sensebox/senseBox-MCU-S2-ESP32S2/examples/icm20948/icm20948.ino

/***************************************************************************
* Example sketch for the ICM20948_WE library
*
* This sketch shows how to setup the accelerometer and how to query accelerometer
* related data. 
* 
* Further information can be found on:
*
* https://wolles-elektronikkiste.de/icm-20948-9-achsensensor-teil-i (German)
* https://wolles-elektronikkiste.de/en/icm-20948-9-axis-sensor-part-i (English)
* 
***************************************************************************/

#include <Wire.h>
#include <ICM20948_WE.h>
#define ICM20948_ADDR 0x68

/* There are several ways to create your ICM20948 object:
 * ICM20948_WE myIMU = ICM20948_WE()              -> uses Wire / I2C Address = 0x68
 * ICM20948_WE myIMU = ICM20948_WE(ICM20948_ADDR) -> uses Wire / ICM20948_ADDR
 * ICM20948_WE myIMU = ICM20948_WE(&wire2)        -> uses the TwoWire object wire2 / ICM20948_ADDR
 * ICM20948_WE myIMU = ICM20948_WE(&wire2, ICM20948_ADDR) -> all together
 * ICM20948_WE myIMU = ICM20948_WE(CS_PIN, spi);  -> uses SPI, spi is just a flag, see SPI example
 * ICM20948_WE myIMU = ICM20948_WE(&SPI, CS_PIN, spi);  -> uses SPI / passes the SPI object, spi is just a flag, see SPI example
 */
ICM20948_WE myIMU = ICM20948_WE(ICM20948_ADDR);
#define I2C_PIN_SCL 42
#define I2C_PIN_SDA 45

void setup() {
  Wire.begin(I2C_PIN_SDA, I2C_PIN_SCL);
  Serial.begin(115200);
  while(!Serial) {}
  
  if(!myIMU.init()){
    Serial.println("ICM20948 does not respond");
  }
  else{
    Serial.println("ICM20948 is connected");
  }

  /*  This is a method to calibrate. You have to determine the minimum and maximum 
   *  raw acceleration values of the axes determined in the range +/- 2 g. 
   *  You call the function as follows: setAccOffsets(xMin,xMax,yMin,yMax,zMin,zMax);
   *  The parameters are floats. 
   *  The calibration changes the slope / ratio of raw acceleration vs g. The zero point 
   *  is set as (min + max)/2.
   */
  //myIMU.setAccOffsets(-16330.0, 16450.0, -16600.0, 16180.0, -16640.0, 16560.0);
    
  /* The starting point, if you position the ICM20948 flat, is not necessarily 0g/0g/1g for x/y/z. 
   * The autoOffset function measures offset. It assumes your ICM20948 is positioned flat with its 
   * x,y-plane. The more you deviate from this, the less accurate will be your results.
   * It overwrites the zero points of setAccOffsets, but keeps the correction of the slope.
   * The function also measures the offset of the gyroscope data. The gyroscope offset does not   
   * depend on the positioning.
   * This function needs to be called after setAccOffsets but before other settings since 
   * it will overwrite settings!
   */
  Serial.println("Position your ICM20948 flat and don't move it - calibrating...");
  delay(1000);
  myIMU.autoOffsets();
  Serial.println("Done!"); 
  
  /* enables or disables the acceleration sensor, default: enabled */
  // myIMU.enableAcc(true);

  /*  ICM20948_ACC_RANGE_2G      2 g   (default)
   *  ICM20948_ACC_RANGE_4G      4 g
   *  ICM20948_ACC_RANGE_8G      8 g   
   *  ICM20948_ACC_RANGE_16G    16 g
   */
  myIMU.setAccRange(ICM20948_ACC_RANGE_2G);
  
  /*  Choose a level for the Digital Low Pass Filter or switch it off.  
   *  ICM20948_DLPF_0, ICM20948_DLPF_2, ...... ICM20948_DLPF_7, ICM20948_DLPF_OFF 
   *  
   *  DLPF       3dB Bandwidth [Hz]      Output Rate [Hz]
   *    0              246.0               1125/(1+ASRD) (default)
   *    1              246.0               1125/(1+ASRD)
   *    2              111.4               1125/(1+ASRD)
   *    3               50.4               1125/(1+ASRD)
   *    4               23.9               1125/(1+ASRD)
   *    5               11.5               1125/(1+ASRD)
   *    6                5.7               1125/(1+ASRD) 
   *    7              473.0               1125/(1+ASRD)
   *    OFF           1209.0               4500
   *    
   *    ASRD = Accelerometer Sample Rate Divider (0...4095)
   *    You achieve lowest noise using level 6  
   */
  myIMU.setAccDLPF(ICM20948_DLPF_6);    
  
  /*  Acceleration sample rate divider divides the output rate of the accelerometer.
   *  Sample rate = Basic sample rate / (1 + divider) 
   *  It can only be applied if the corresponding DLPF is not off!
   *  Divider is a number 0...4095 (different range compared to gyroscope)
   *  If sample rates are set for the accelerometer and the gyroscope, the gyroscope
   *  sample rate has priority.
   */
  myIMU.setAccSampleRateDivider(10);
}

void loop() {
  myIMU.readSensor();
  xyzFloat accRaw = myIMU.getAccRawValues();
  xyzFloat corrAccRaw = myIMU.getCorrectedAccRawValues();
  xyzFloat gVal = myIMU.getGValues();
  float resultantG = myIMU.getResultantG(gVal);

   
  Serial.println("Raw acceleration values (x,y,z):");
  Serial.print(accRaw.x);
  Serial.print("   ");
  Serial.print(accRaw.y);
  Serial.print("   ");
  Serial.println(accRaw.z);

  Serial.println("Corrected raw acceleration values (x,y,z):");
  Serial.print(corrAccRaw.x);
  Serial.print("   ");
  Serial.print(corrAccRaw.y);
  Serial.print("   ");
  Serial.println(corrAccRaw.z);

  Serial.println("g-values (x,y,z):");
  Serial.print(gVal.x);
  Serial.print("   ");
  Serial.print(gVal.y);
  Serial.print("   ");
  Serial.println(gVal.z);

  Serial.print("Resultant g: ");
  Serial.println(resultantG);
  Serial.println("*************************************");
 
  delay(1000);
}
