sensebox/senseBox-MCU-S2-ESP32S2/examples/homeV2/ids.h

char *SENSEBOX_ID="";
char *TEMP_ID="";
char *HUMI_ID="";
char *PRESSURE_ID="";
char *LUX_ID="";
char *UV_ID="";
char *PM1_ID="";
char *PM25_ID="";
char *PM4_ID="";
char *PM10_ID="";
char *RAINEVENT_ID="";
char *RAININTENSITY_ID="";
char *RAINTOTALACC_ID="";
char *ACCESS_TOKEN="";
